azerty220/2526_Maker_Drumled/rendus_option_maker_hors_projet/cao/fusion2_5design.png

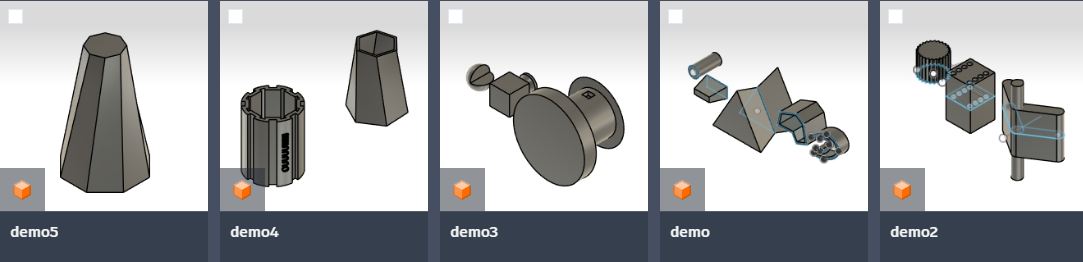
rendus_option_maker_hors_projet/cao/fusion2_5design.png
