azerty220/2526_Maker_Drumled/support photo video/photo_pcb1.jpeg

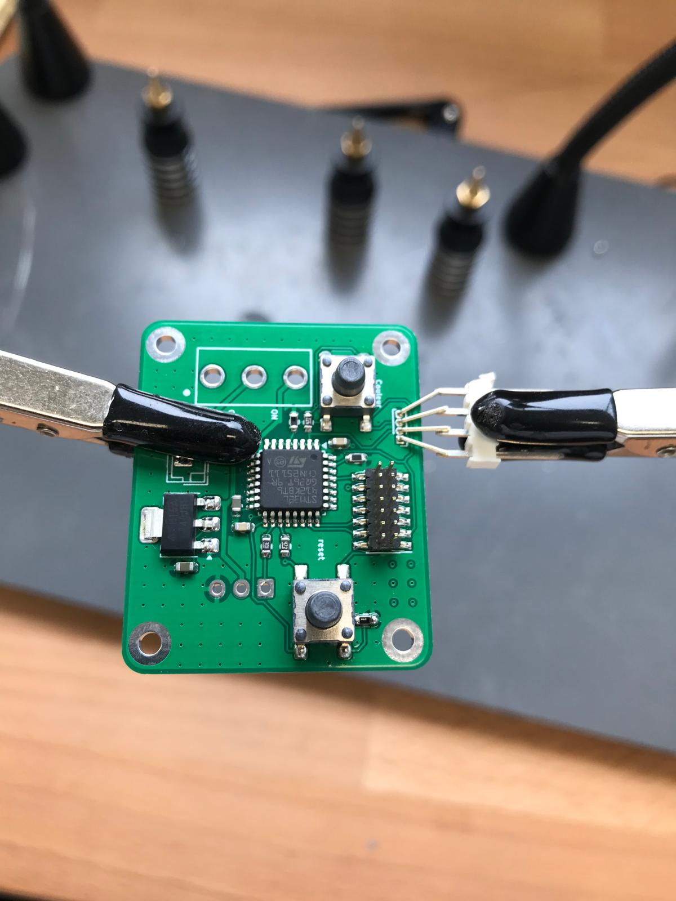
support photo video/photo_pcb1.jpeg
