azerty220/2526_Maker_Drumled/support photo video/photo_pcb2.jpeg

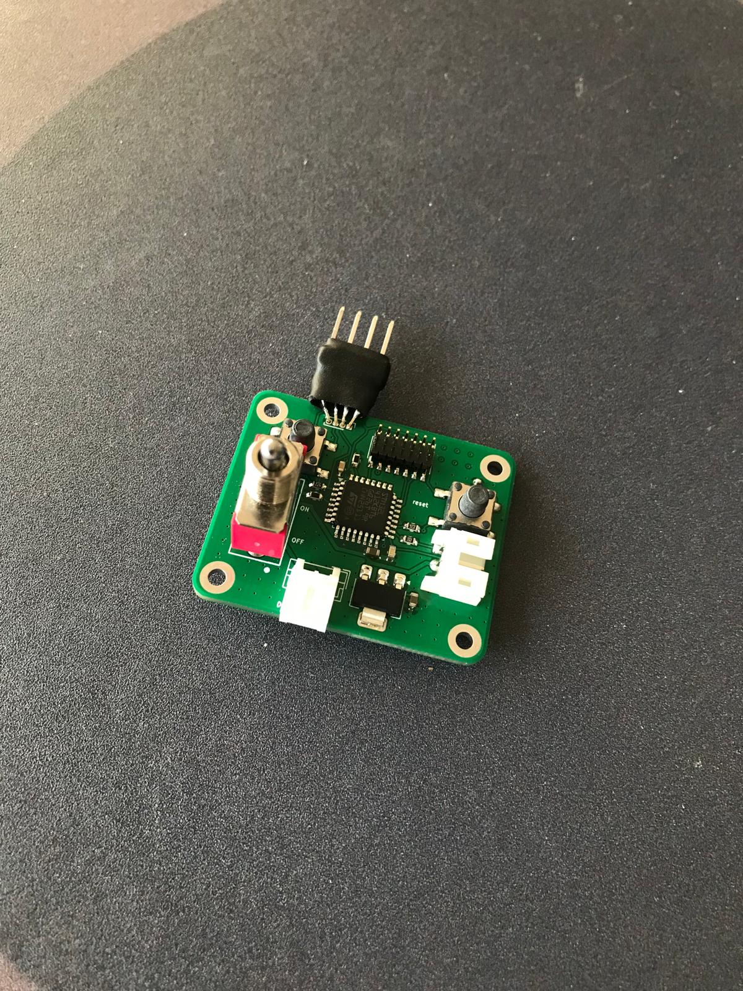
support photo video/photo_pcb2.jpeg
