azerty220/2526_Maker_Drumled/rendus_option_maker_hors_projet/cao/exercice1.png

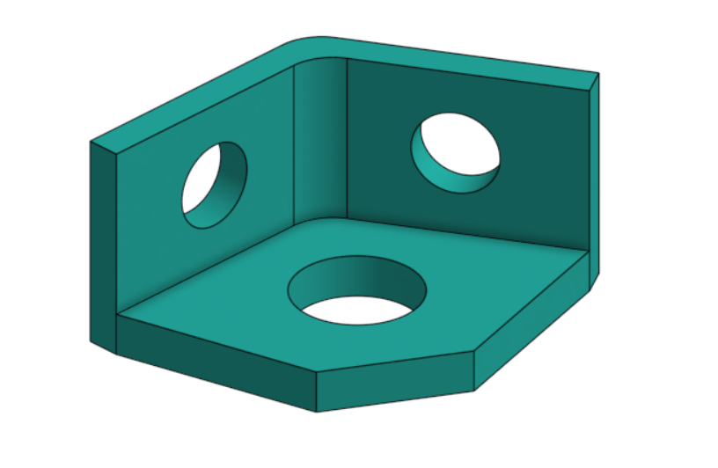
rendus_option_maker_hors_projet/cao/exercice1.png
