azerty220/2526_Maker_Drumled/rendus_option_maker_hors_projet/cao/fait_en_amont_en_cao.jpeg

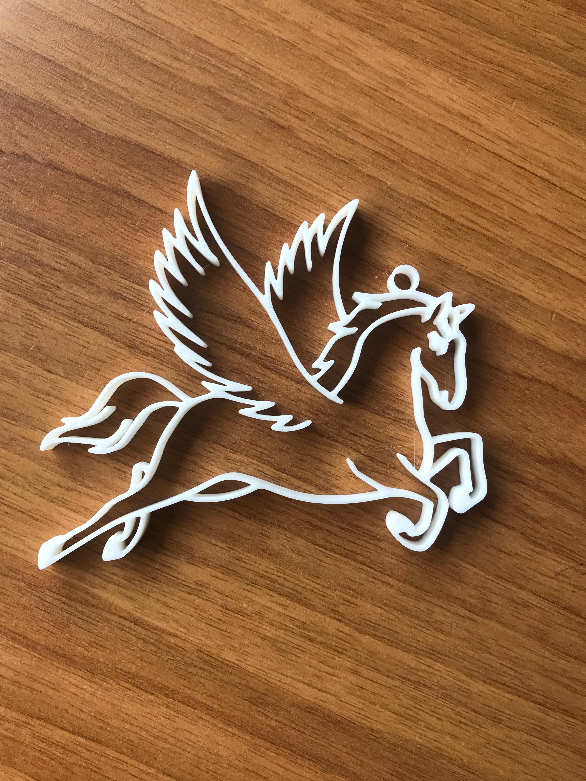
rendus_option_maker_hors_projet/cao/fait_en_amont_en_cao.jpeg
