azerty220/2526_Maker_Drumled/rendus_option_maker_hors_projet/couture/bandeau.jpeg

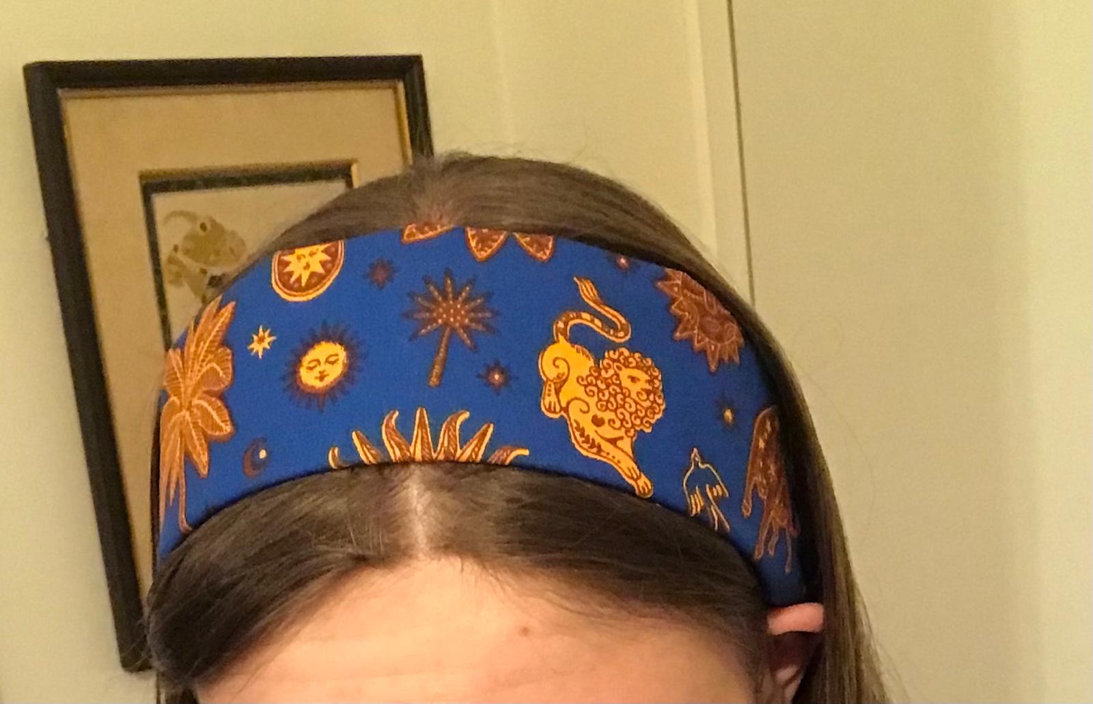
rendus_option_maker_hors_projet/couture/bandeau.jpeg
