azerty220/2526_Maker_Drumled/rendus_option_maker_hors_projet/couture/pochette4.jpeg

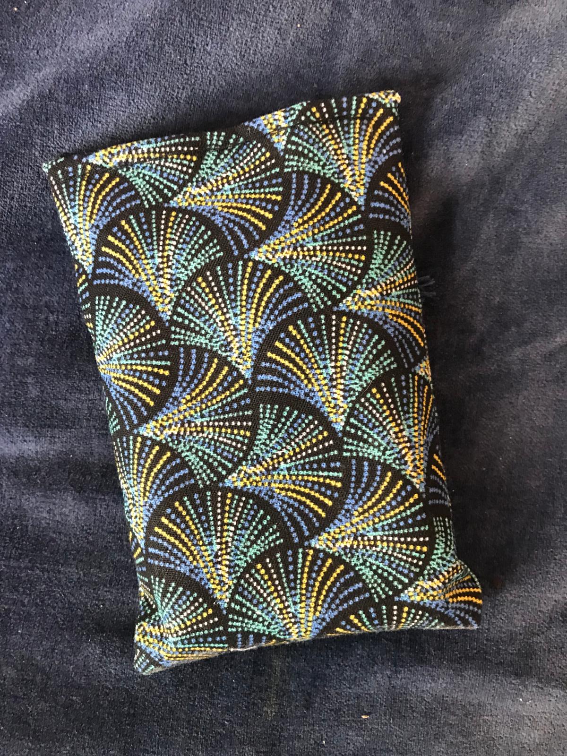
rendus_option_maker_hors_projet/couture/pochette4.jpeg
