azerty220/2526_Maker_Drumled/rendus_option_maker_hors_projet/couture/tissu_marche_st_pierre.jpeg

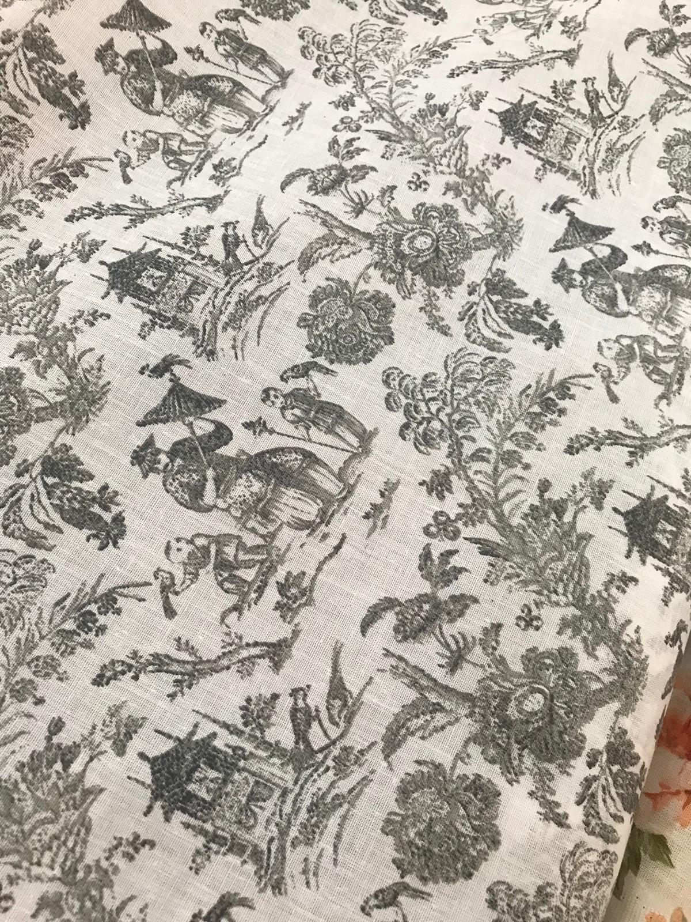
rendus_option_maker_hors_projet/couture/tissu_marche_st_pierre.jpeg
