azerty220/2526_Maker_Drumled/rendus_option_maker_hors_projet/impression 3D/porte_clef.jpeg

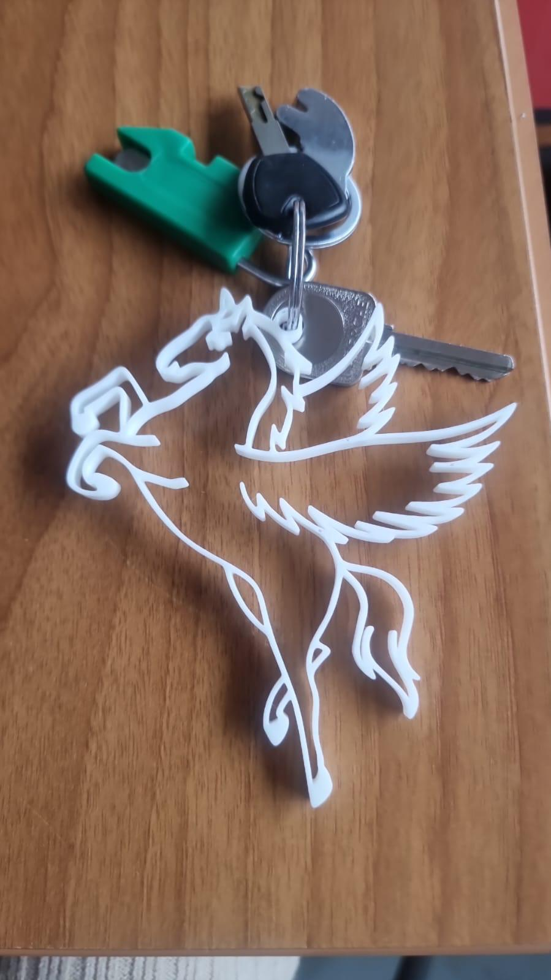
rendus_option_maker_hors_projet/impression 3D/porte_clef.jpeg
