azerty220/2526_Maker_Drumled/rendus_option_maker_hors_projet/pcb/pcb hackathon/schematique.jpeg

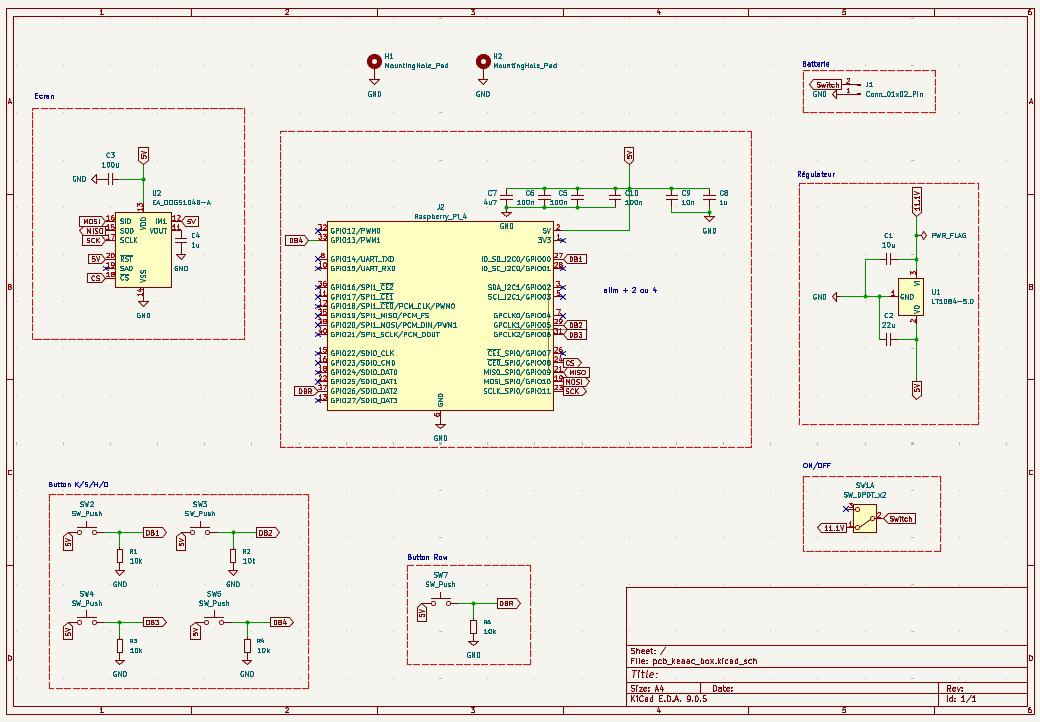
rendus_option_maker_hors_projet/pcb/pcb hackathon/schematique.jpeg
