azerty220/2526_Maker_Drumled/rendus_option_maker_hors_projet/pcb/pcb/schematique2.png

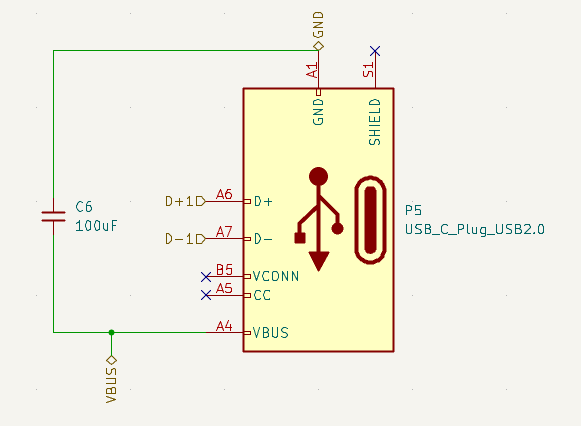
rendus_option_maker_hors_projet/pcb/pcb/schematique2.png
