azerty220/2526_Maker_Drumled/rendus_option_maker_hors_projet/pcb/pcb/schematique.png

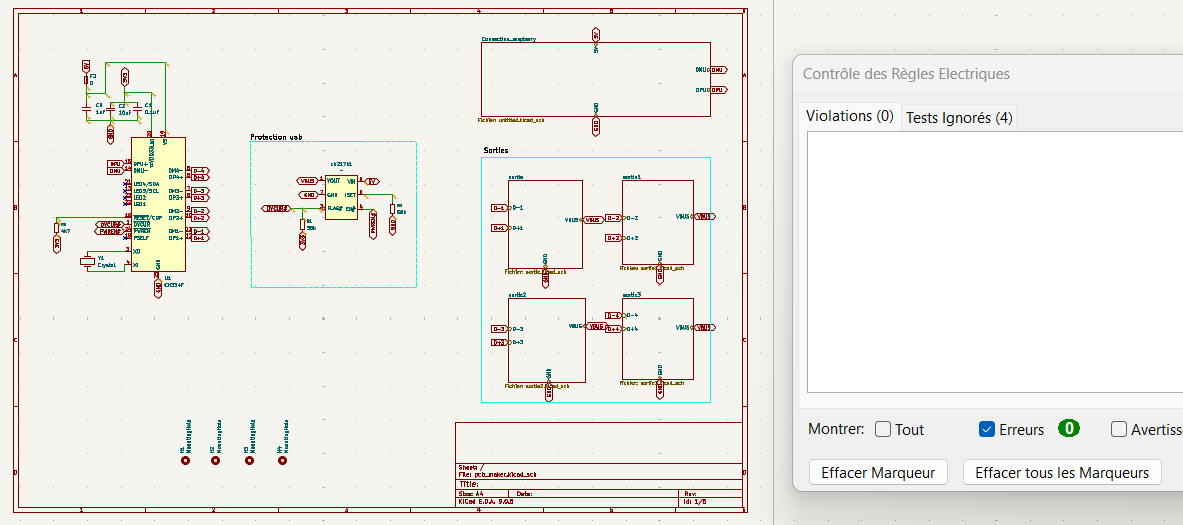
rendus_option_maker_hors_projet/pcb/pcb/schematique.png
